haohaohaoyan/goofy-ahh-epaper-watch/PCB/silkscreens/background.png

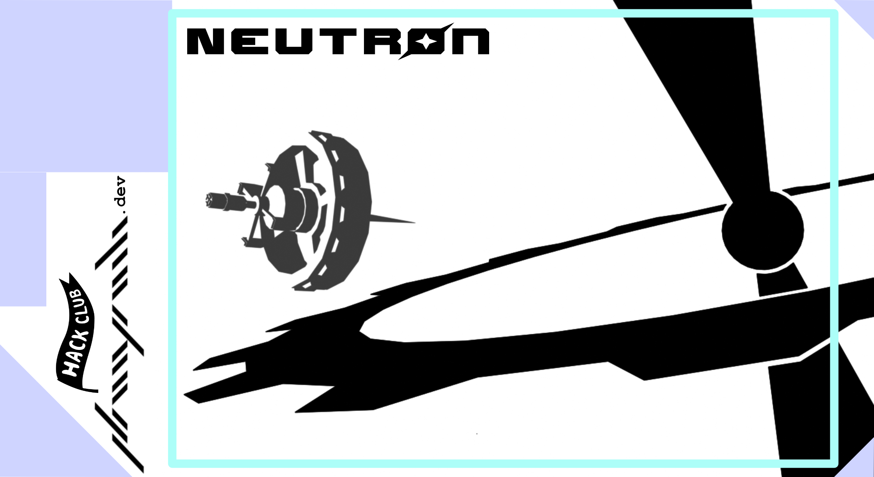
PCB/silkscreens/background.png
