haohaohaoyan/goofy-ahh-epaper-watch/PCB/silkscreens/bgartbase.png

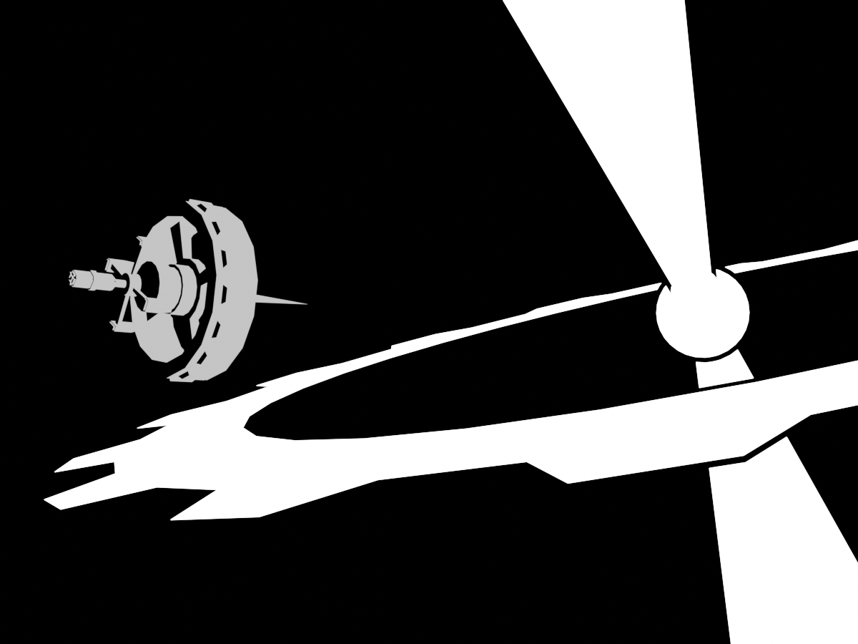
PCB/silkscreens/bgartbase.png
