haohaohaoyan/goofy-ahh-epaper-watch/Journal/06-10-26.png

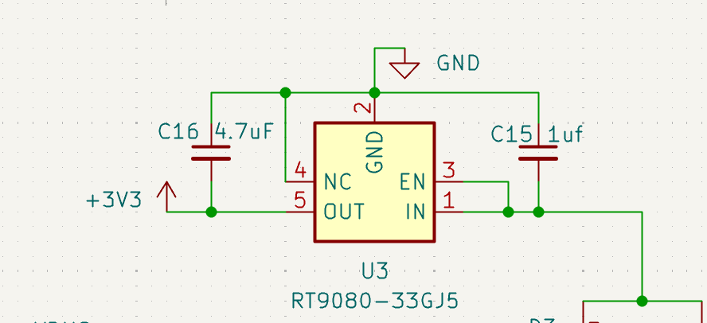
Journal/06-10-26.png
